hb020/batterymeter/doc/CN0510/EVAL-ADICUP3029/EVAL_ADICUP3029_ID.pdf

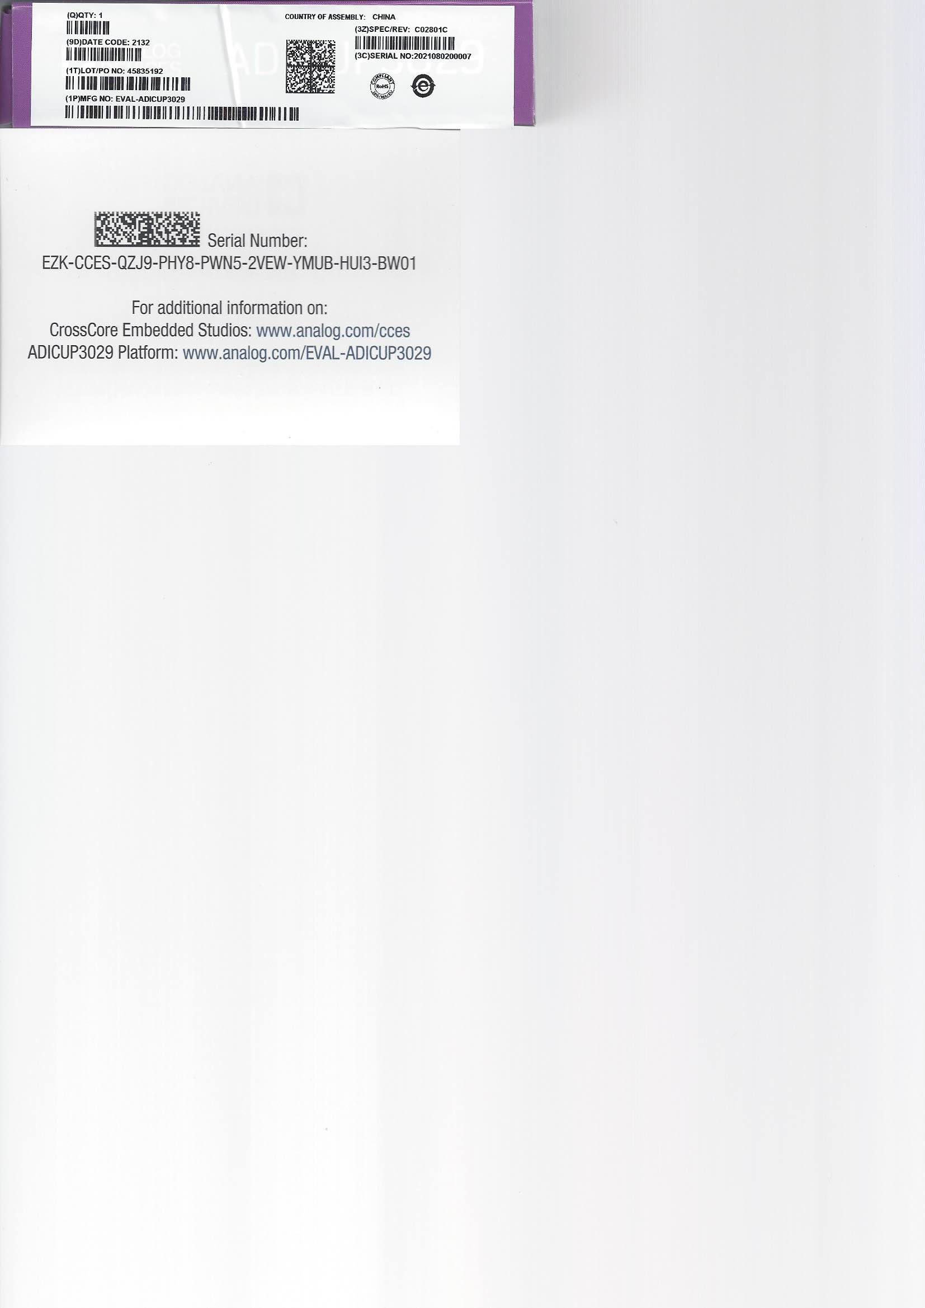
[picture p9: page 1]
