hb020/batterymeter/img/CN0510_06_1024.jpg

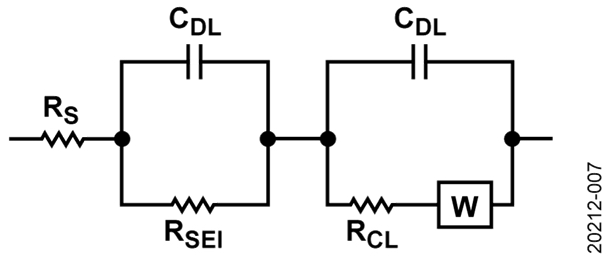
img/CN0510_06_1024.jpg
