hb020/batterymeter/img/pogo-R100-1W.jpg

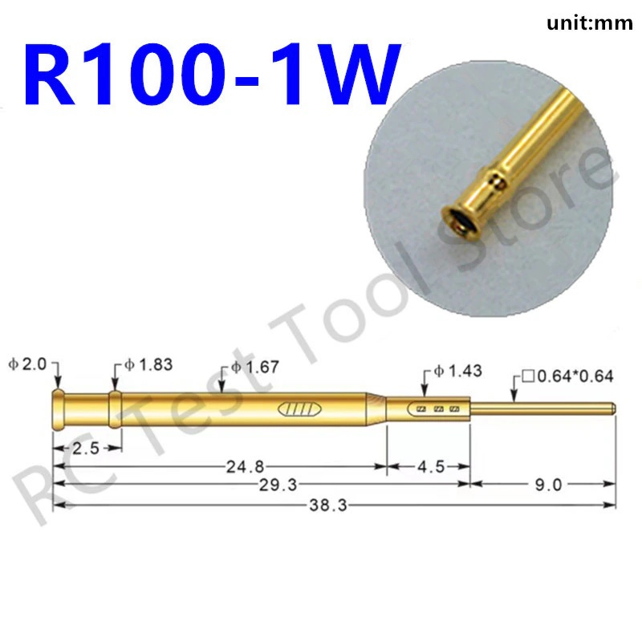
img/pogo-R100-1W.jpg
