hb020/batterymeter/doc/components/oled_128x32/11111782823_523352349.jpeg

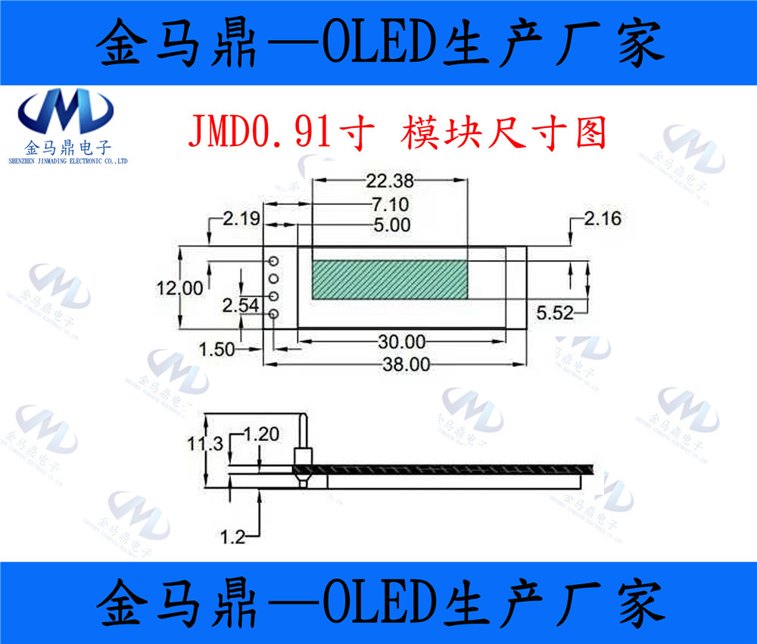
doc/components/oled_128x32/11111782823_523352349.jpeg
