hb020/batterymeter/doc/components/oled_128x32/19966762783_523352349.jpeg

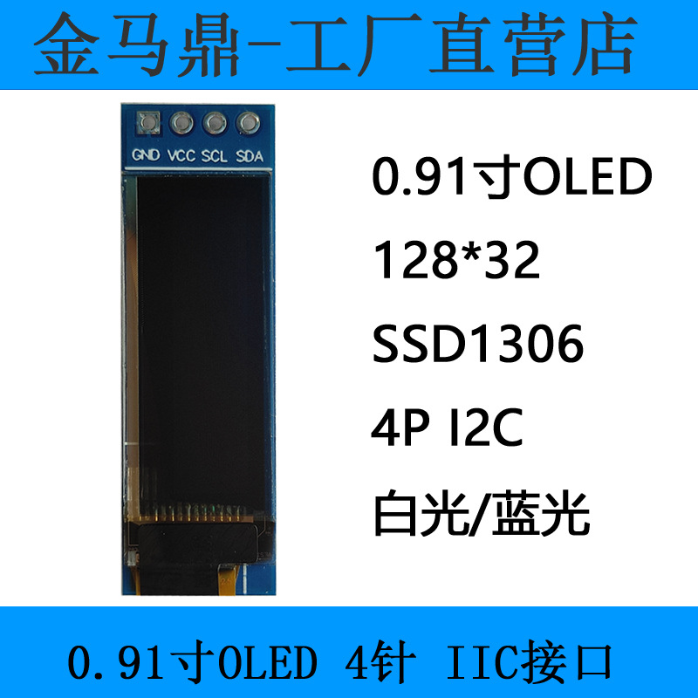
doc/components/oled_128x32/19966762783_523352349.jpeg
