hb020/batterymeter/doc/CN0510/CN0510-DesignSupport/01-047456-01-d.pdf

## ART FILM - assy1

D

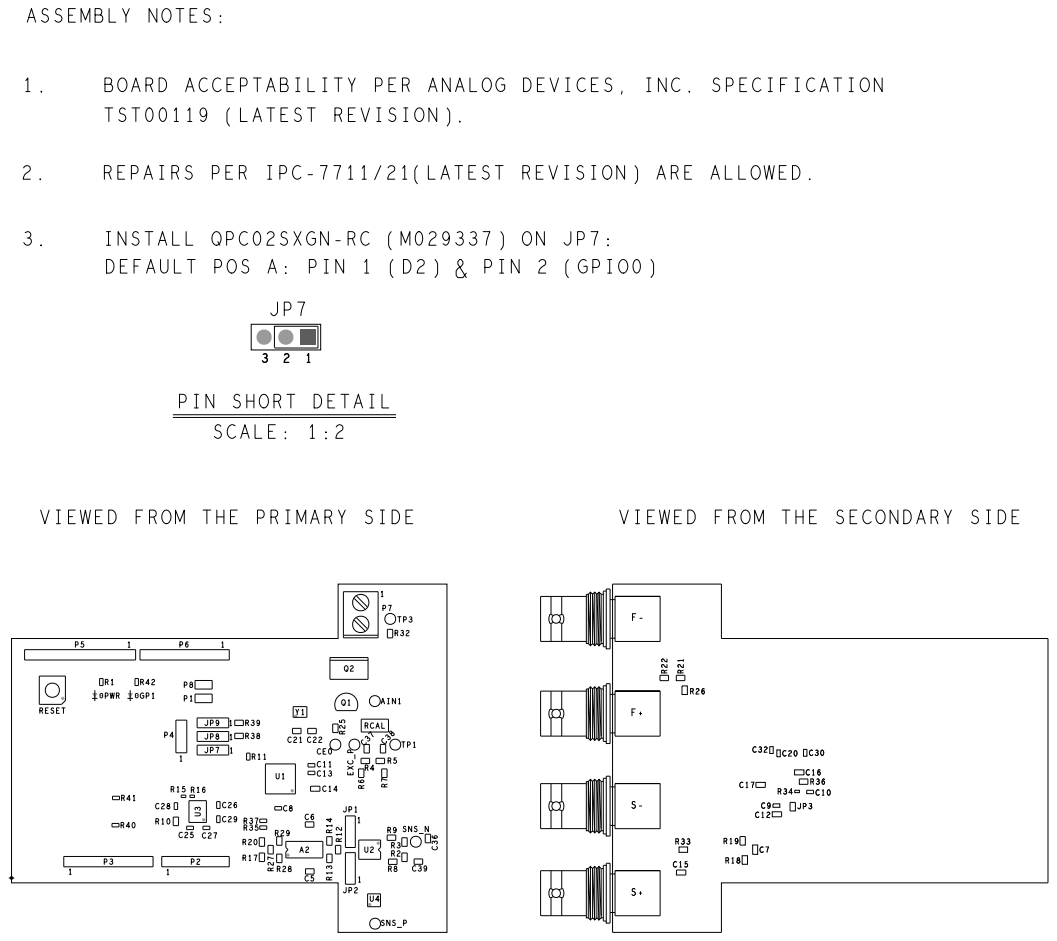
[picture p24: page 1]

REVISIONS

REV | DESCRIPTION | | | DATE | | APPROVED
A | INITIAL RELEASE | | | | 30JAN18 | C.DENG
B | AS PER ECR-078094 | | | | 21MAY18 | C.DENG
C | PER ECR-084889 | 01MAR19 | P SHEAHAN

D | PER ECR-089796 | 16AUG19 | P SHEAHAN

DEFAULT POS A: PIN 1 (D2) & PIN 2 (GPIO0)

VIEWED FROM THE PRIMARY SIDE

VIEWED FROM THE SECONDARY SIDE

UNLESS OTHERWISE SPECIFIED DECIMALS .XX +-.010 .XXX +-.005 .XXXX +-.0050 | TOLERANCES FRACTIONS +-1/32 | ANGLES +- 2 | APPROVAL | DATE

TEMPLATE ENGINEER N/A
HARDWARE SERVICES P SHEAHAN | 16AUG19

MATERIAL | TEST ENGINEER N/A

COMPONENT ENGINEER N/A

TEST PROCESS N/A
HARDWARE RELEASE P SHEAHAN | 16AUG19
DESIGNER M LAMBE | 16AUG19 | SIZE C | FSCM NO 24355 | DRAWING NUMBER 01 | -047456 | REV D
PTD ENGINEER M LAMBE | 16AUG19

CHECKER N/A

DO NOT SCALE DWG | | 1/1 SCALE | | SHEET
