hb020/batterymeter/doc/CN0510/CN0510-DesignSupport/08-047456-01-d.pdf

## ART FILM - silk_prm

047456

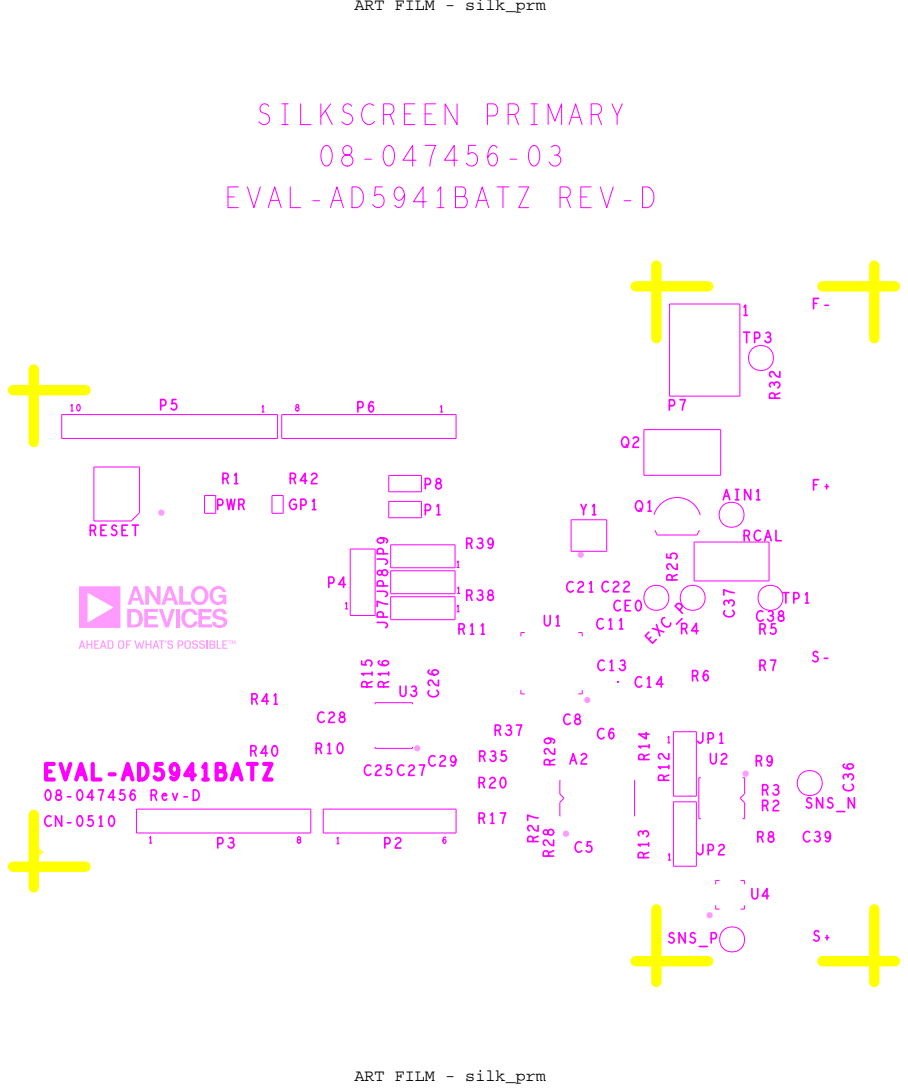
[picture p25: page 1]

## ART FILM - l1_primary

047456

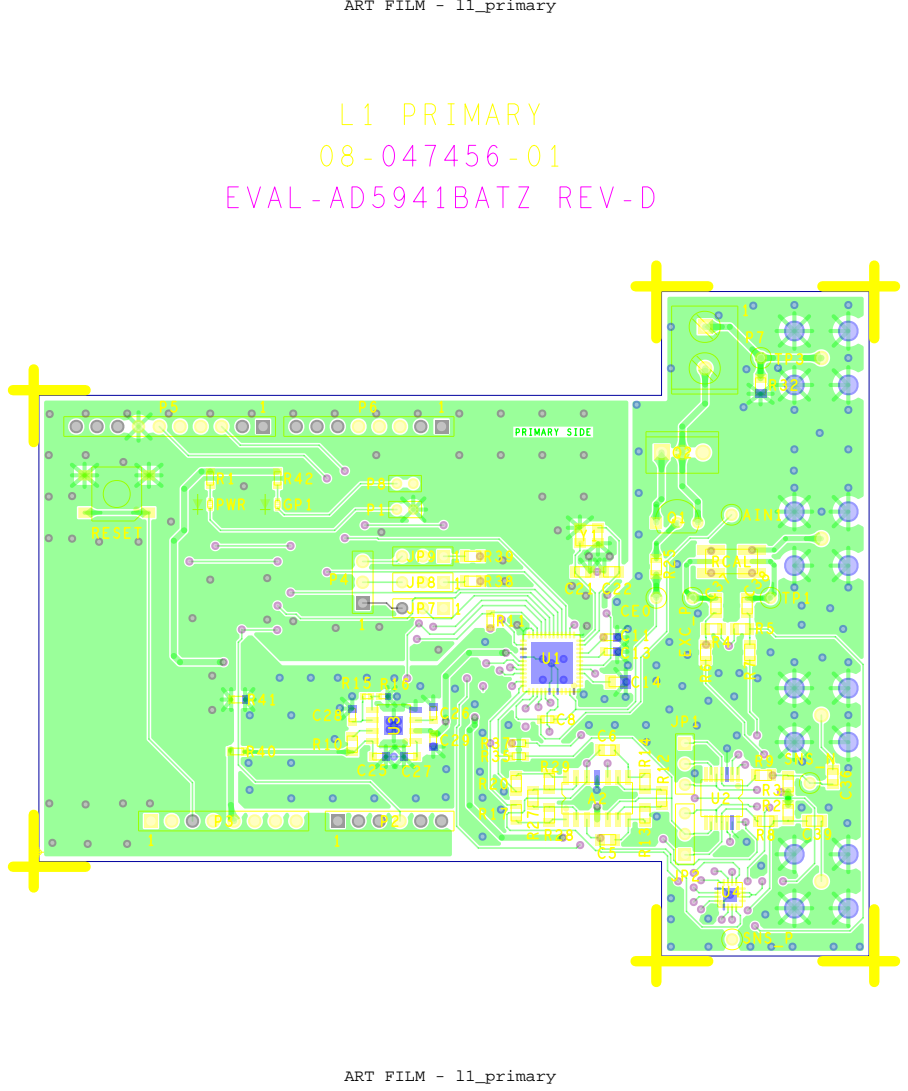
[picture p26: page 2]

## ART FILM - l2_secondary

047456

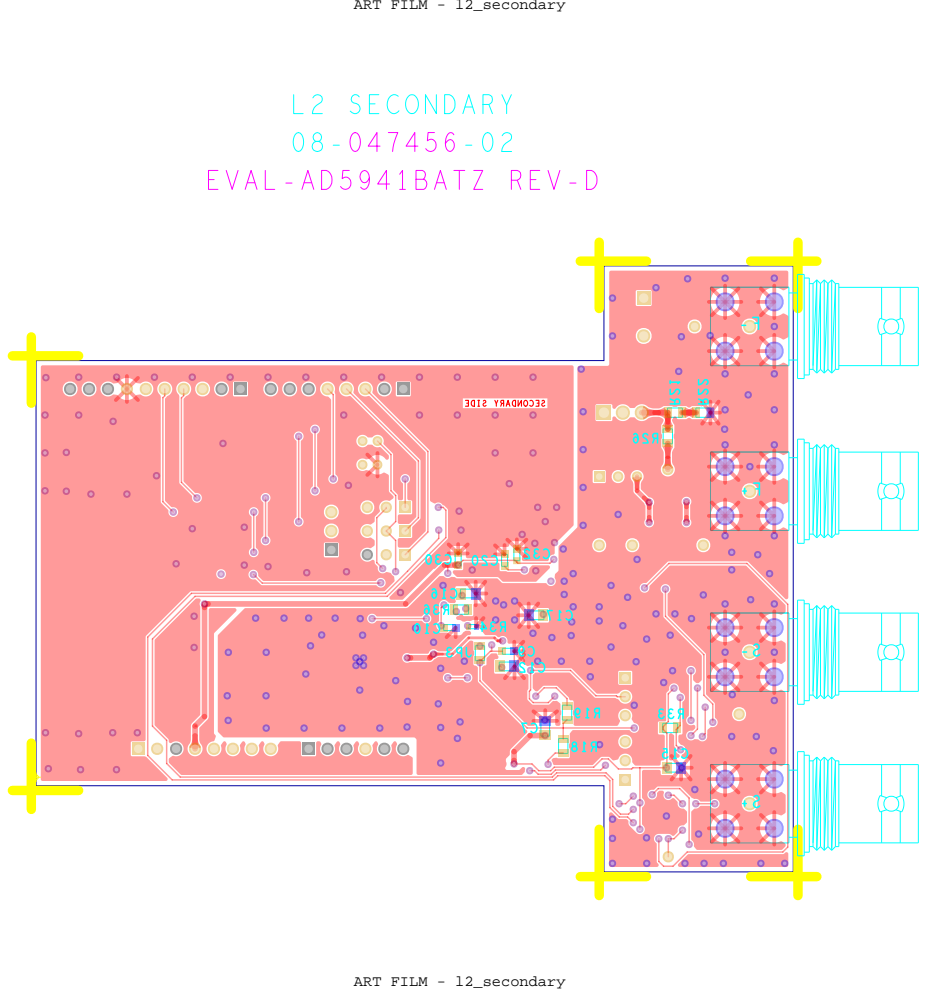
[picture p27: page 3]

## ART FILM - silk_sec

047456

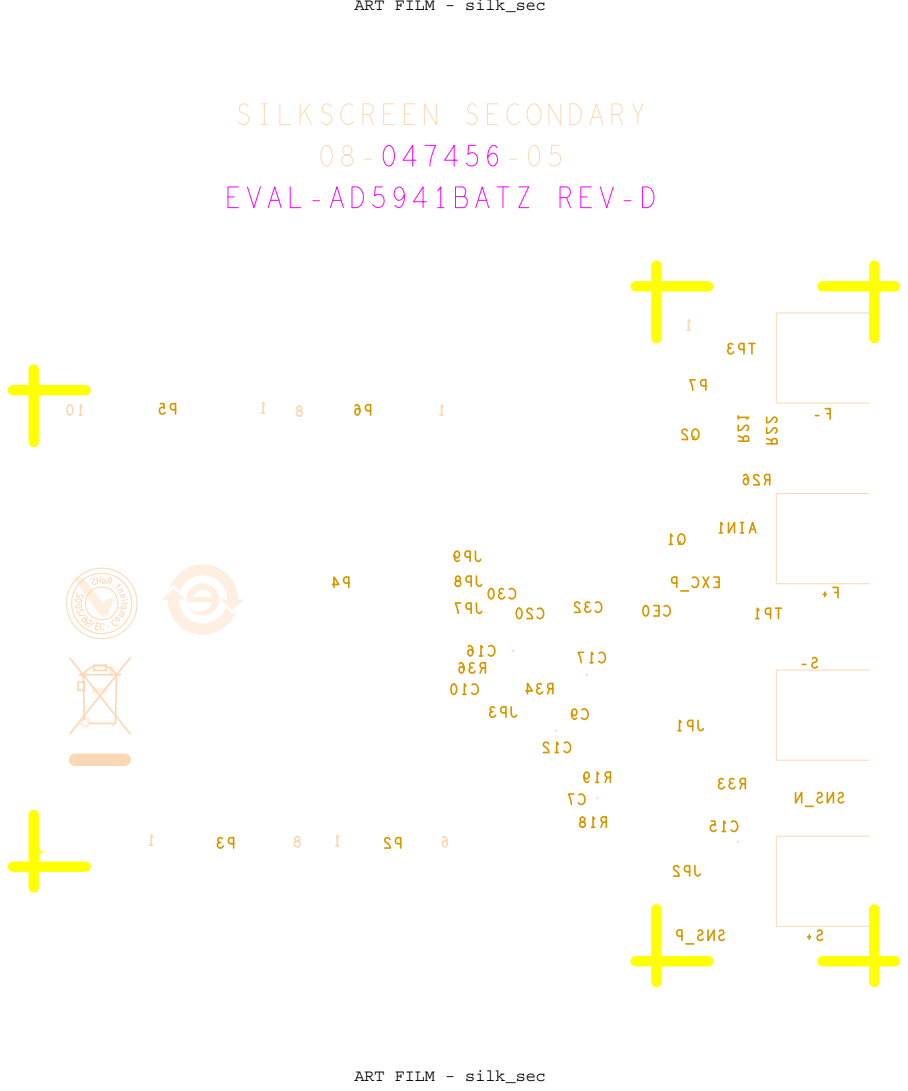
[picture p28: page 4]

## ART FILM - mask_prm

08- | -04 047456

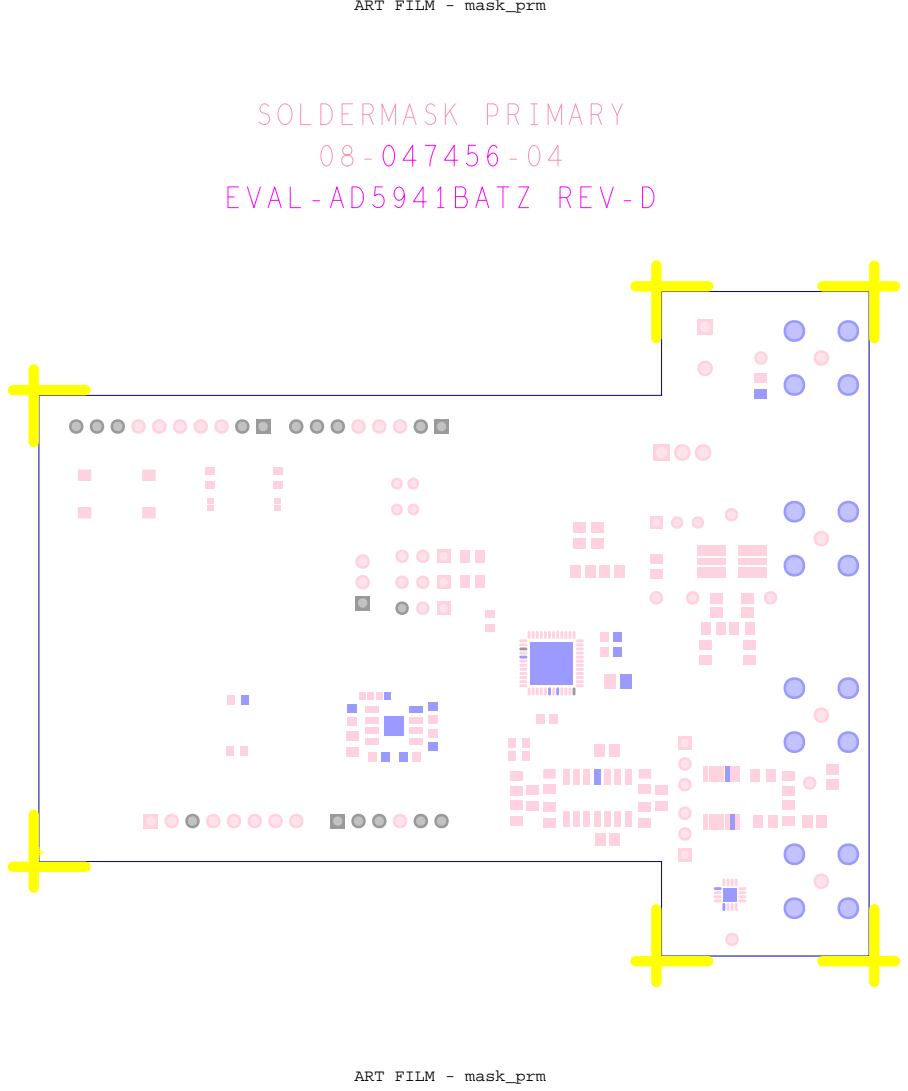
[picture p29: page 5]
ART FILM - mask_prm; SOLDERMASK PRIMARY; EVAL-AD5941BATZ REV-D

## ART FILM - mask_sec

08- | -06 047456

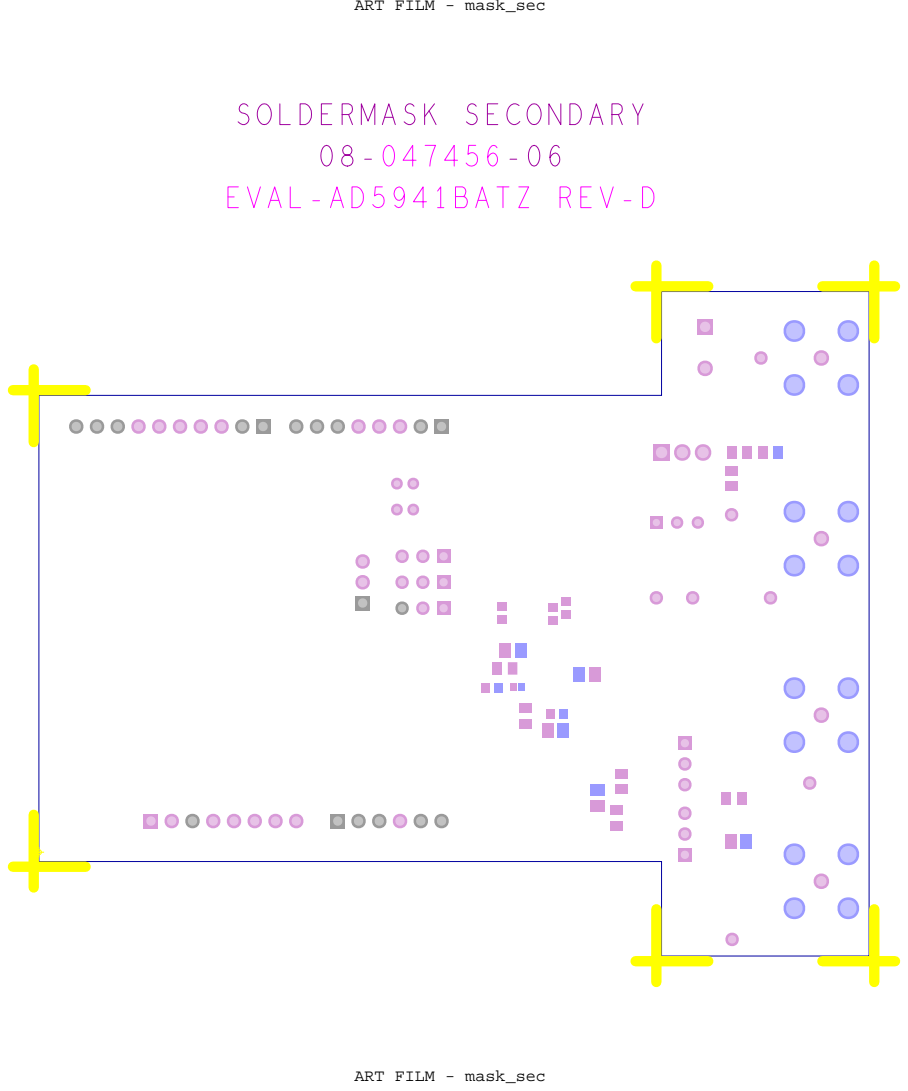
[picture p30: page 6]
ART FILM - mask_sec; SOLDERMASK SECONDARY; EVAL-AD5941BATZ REV-D

## ART FILM - paste_prm

047456

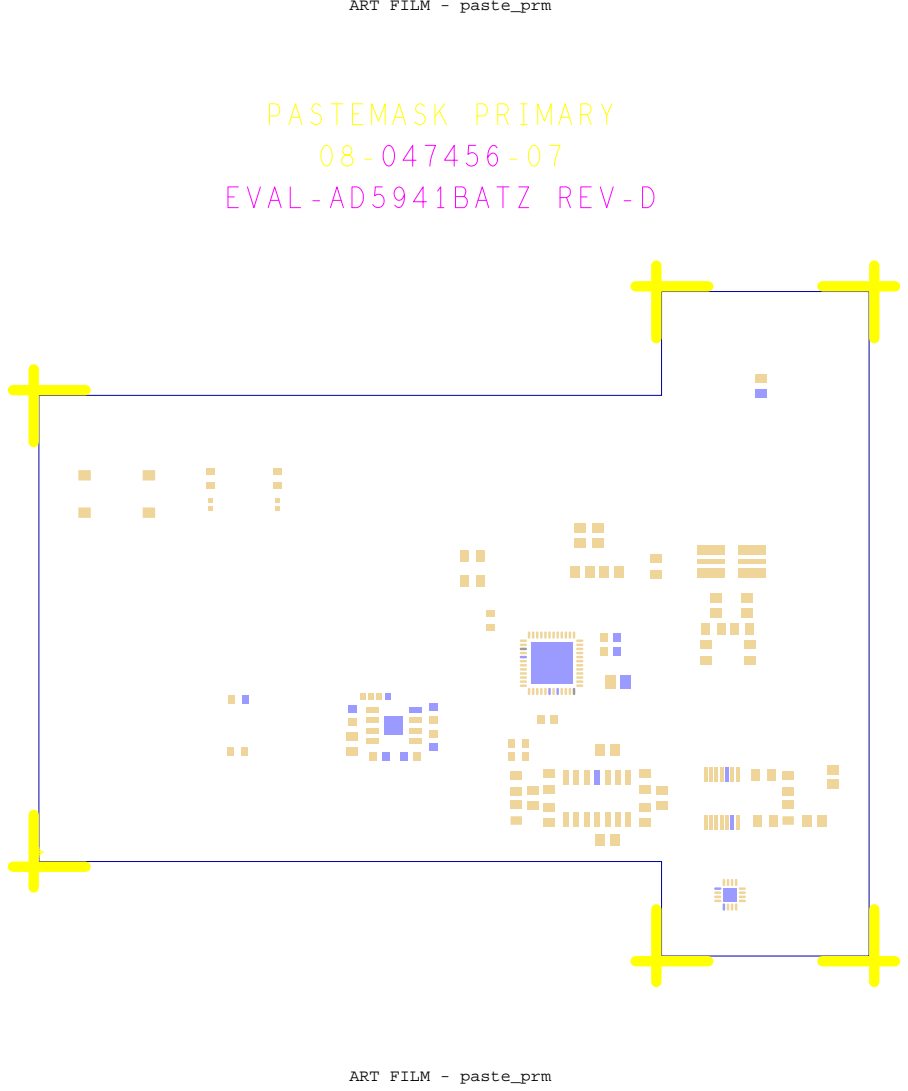
[picture p31: page 7]
ART FILM - paste_prm; PASTEMASK PRIMARY; EVAL-AD5941BATZ REV-D

## ART FILM - paste_sec

## ART FILM - paste_sec

08- | -08 047456

# PASTEMASK SECONDARY

# EVAL-AD5941BATZ REV-D
