hb020/batterymeter/doc/CN0510/CN0510-DesignSupport/09-047456-01-d.pdf

D

1

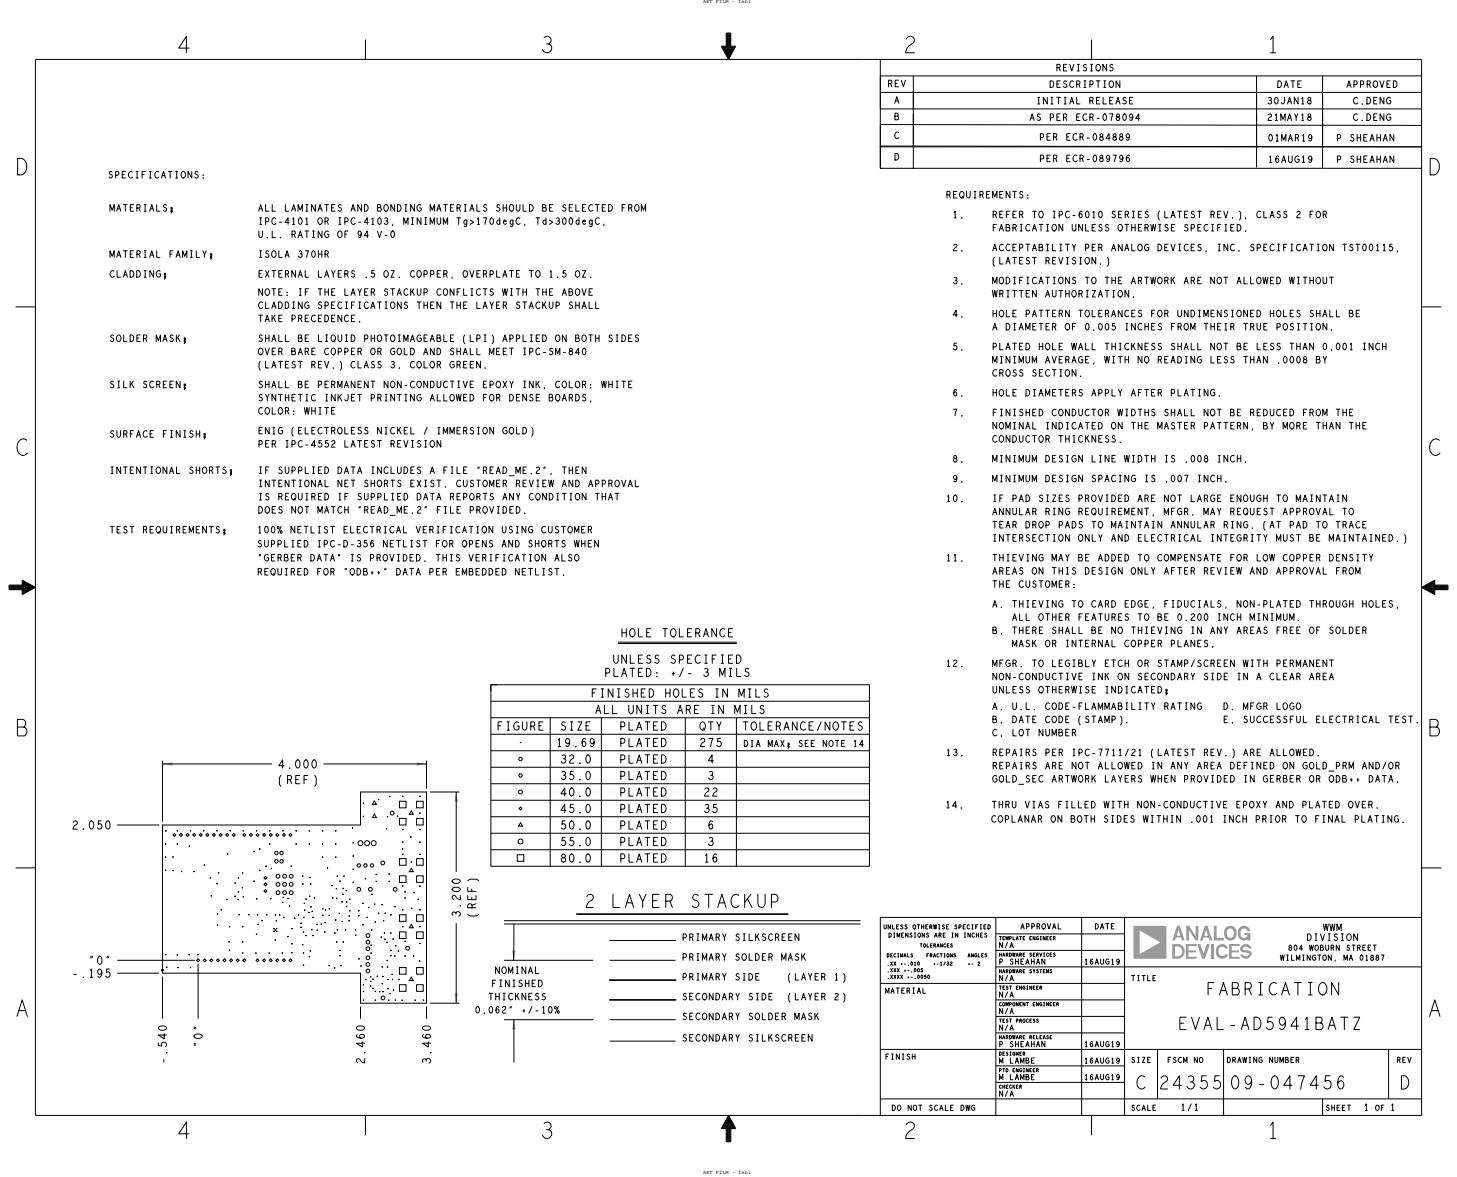
[picture p32: page 1]
ART FILM - fab1; C.DENG; P SHEAHAN; WWM DIVISION 804 WOBURN STREET WILMINGTON, MA 01887; 21MAY18; 01MAR19; 16AUG19; PER ECR-089796; REQUIREMENTS:; REFER; TO IPC-6010 SERIES (LATEST REV.), CLASS 2 FOR; ACCEPTABILITY PER ANALOG DEVICES,; INC. SPECIFICATION; TST00115,; (LATEST REVISION.); MODIFICATIONS; THE ARTWORK ARE NOT ALLOWED WITHOUT; WRITTEN AUTHORIZATION.; HOLE PATTERN; TOLERANCES FOR UNDIMENSIONED; HOLES SHALL BE; A DIAMETER OF 0.005; INCHES FROM; THEIR; TRUE POSITION.; PLATED; HOLE WALL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

REVISIONS

REV | DESCRIPTION | DATE | | APPROVED
A | INITIAL RELEASE | | 30JAN18 | C.DENG

AS PER ECR-078094
PER ECR-084889

ALL LAMINATES AND BONDING MATERIALS SHOULD BE SELECTED FROM
U.L. RATING OF 94 V-0
ISOLA 370HR
TAKE PRECEDENCE.
SHALL BE LIQUID PHOTOIMAGEABLE (LPI) APPLIED ON BOTH SIDES
(LATEST REV.) CLASS 3. COLOR GREEN.
SYNTHETIC INKJET PRINTING ALLOWED FOR DENSE BOARDS,
COLOR: WHITE
PER IPC-4552 LATEST REVISION

FABRICATION UNLESS OTHERWISE SPECIFIED.

6. HOLE DIAMETERS APPLY AFTER PLATING.

INTENTIONAL NET SHORTS EXIST. CUSTOMER REVIEW AND APPROVAL
DOES NOT MATCH "READ_ME.2" FILE PROVIDED.
100% NETLIST ELECTRICAL VERIFICATION USING CUSTOMER
SUPPLIED IPC-D-356 NETLIST FOR OPENS AND SHORTS WHEN
"GERBER DATA" IS PROVIDED. THIS VERIFICATION ALSO
REQUIRED FOR "ODB++" DATA PER EMBEDDED NETLIST.

AREAS ON THIS DESIGN ONLY AFTER REVIEW AND APPROVAL FROM
THE CUSTOMER:

HOLE TOLERANCE
UNLESS SPECIFIED
PLATED: +/- 3 MILS
ALL UNITS ARE IN MILS
PLATED
2 LAYER STACKUP

UNLESS OTHERWISE INDICATED;
C. LOT NUMBER

13. REPAIRS PER IPC-7711/21 (LATEST REV.) ARE ALLOWED.

14. THRU VIAS FILLED WITH NON-CONDUCTIVE EPOXY AND PLATED OVER.

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

PRIMARY SILKSCREEN
PRIMARY SOLDER MASK
SECONDARY SIDE (LAYER 2)
SECONDARY SOLDER MASK

TEMPLATE ENGINEER N/A
HARDWARE SERVICES P SHEAHAN | 16AUG19
HARDWARE SYSTEMS N/A | | | TITLE FABRICATION EVAL-AD5941BATZ

MATERIAL | | TEST ENGINEER N/A

COMPONENT ENGINEER N/A

TEST PROCESS N/A
HARDWARE RELEASE P SHEAHAN | 16AUG19
DESIGNER M LAMBE | 16AUG19 | SIZE C | | FSCM NO 24355 | DRAWING NUMBER 09 | -047456 | REV D
PTD ENGINEER M LAMBE | 16AUG19

CHECKER N/A

DO NOT SCALE DWG | | | 1/1 SCALE | | SHEET
