hb020/batterymeter/kicad/impedance_testboard/impedance_testboard_board.pdf

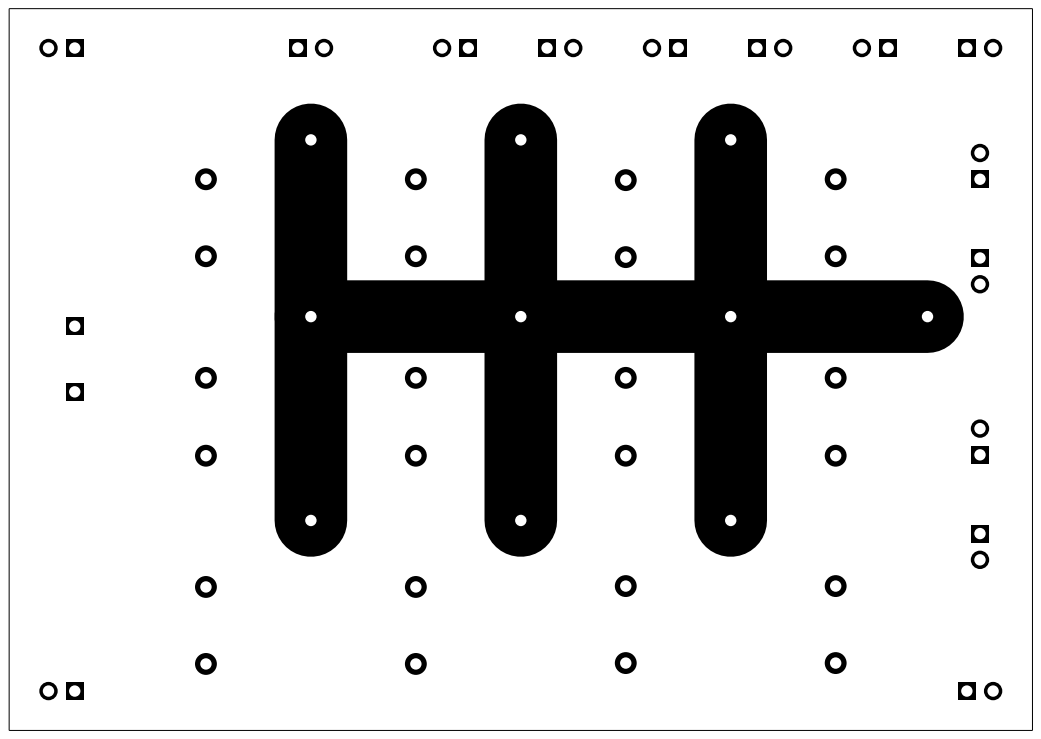
[picture p33: page 1]

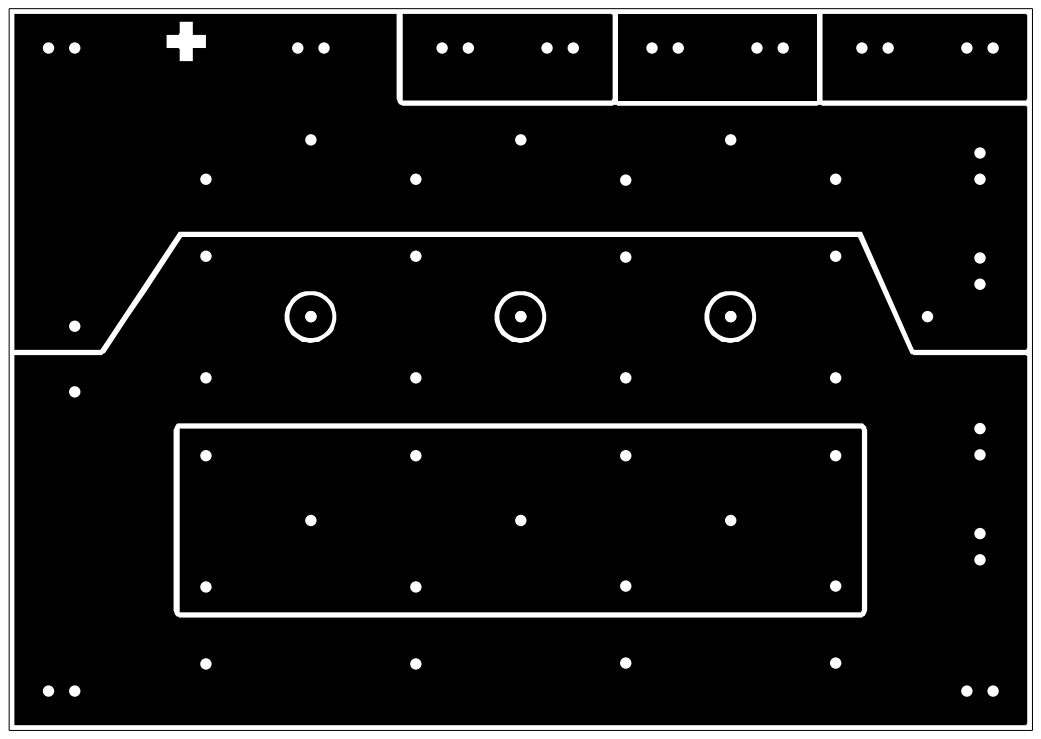
[picture p34: page 2]

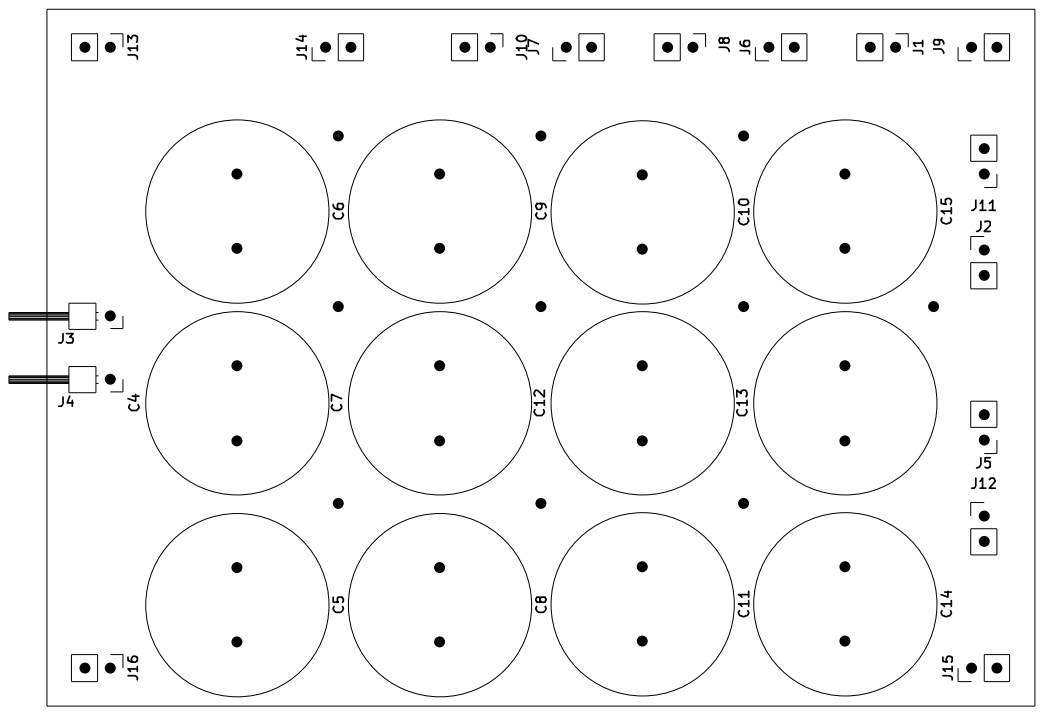
[picture p35: page 3]

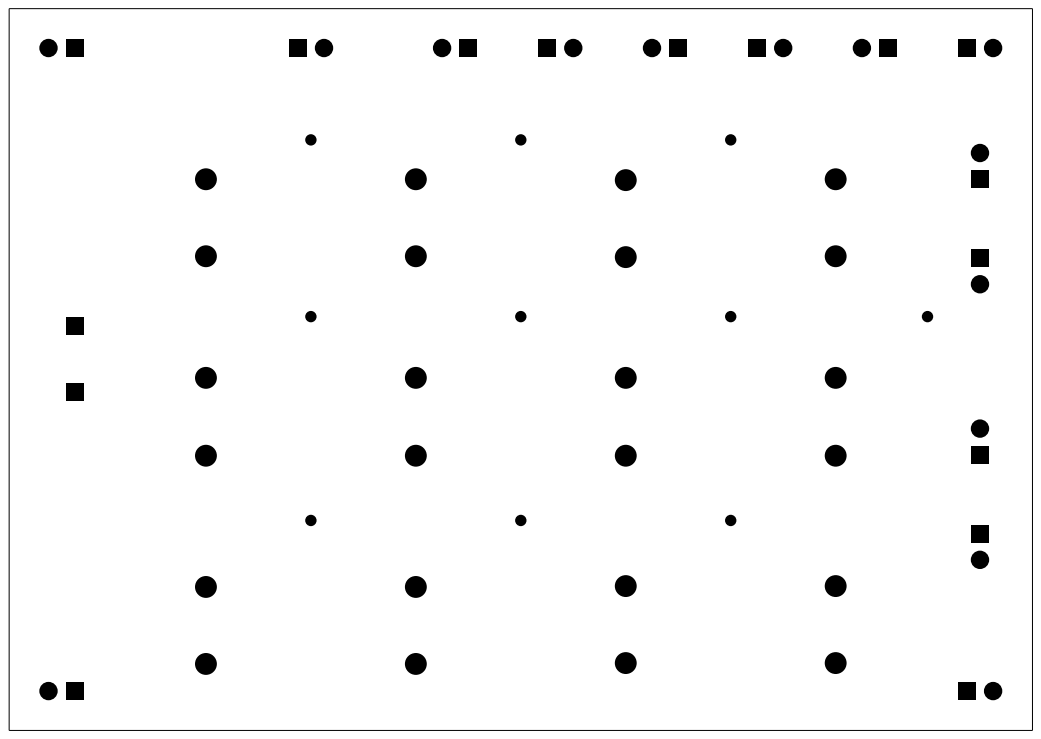
[picture p36: page 4]

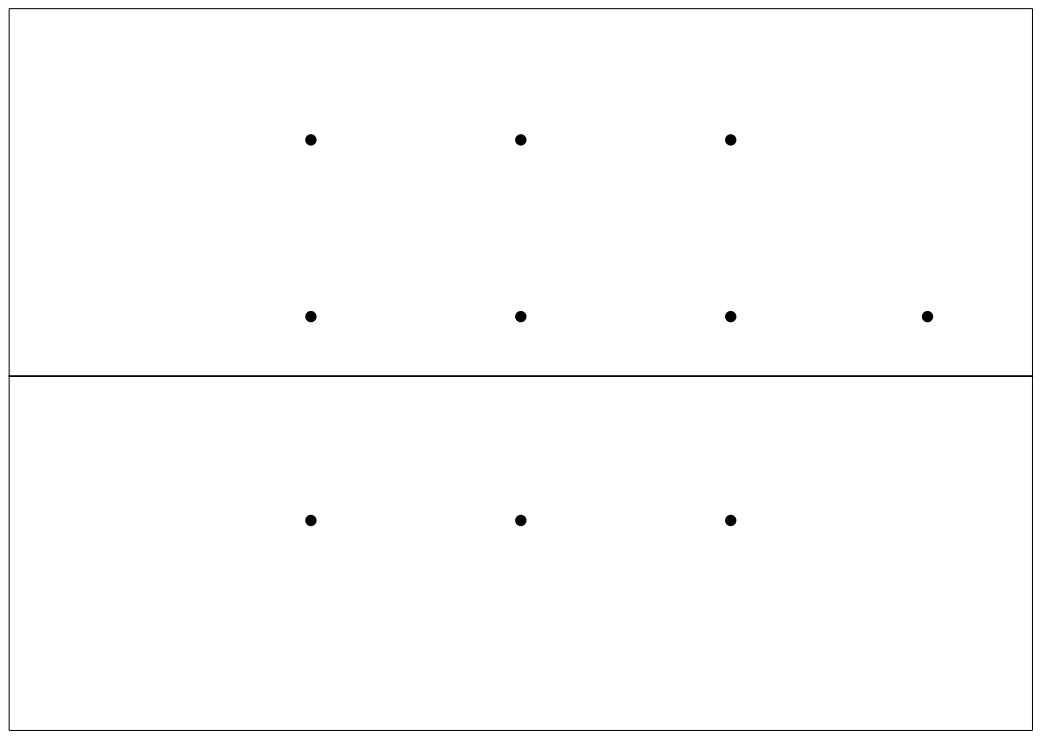
[picture p37: page 5]

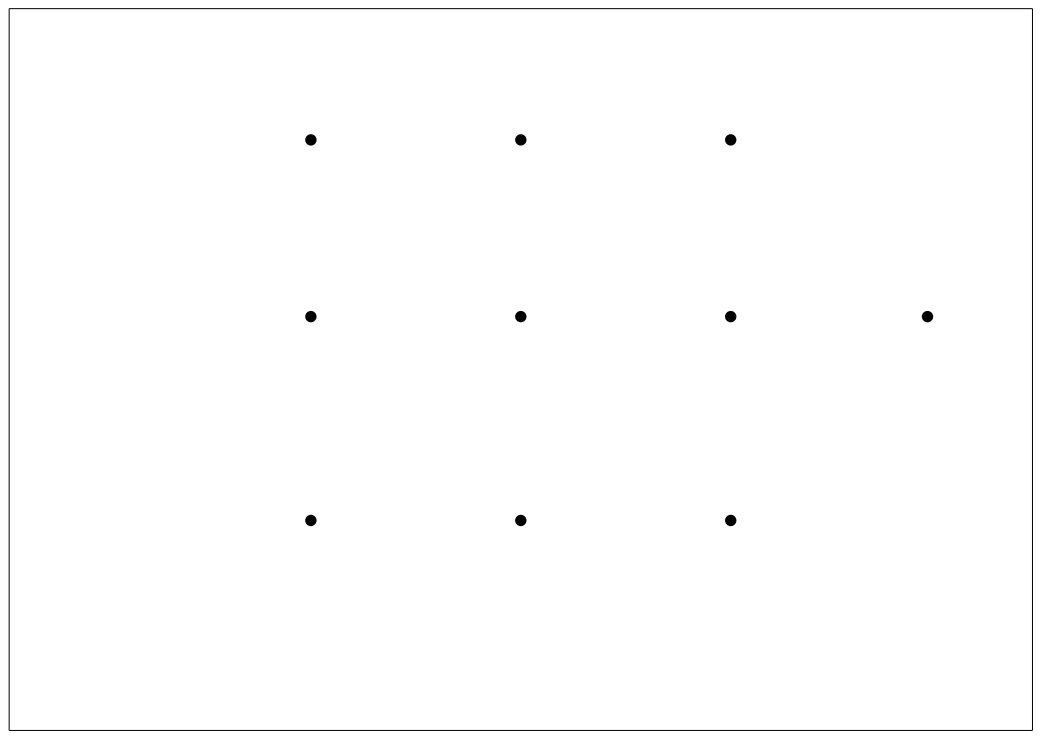
[picture p38: page 6]

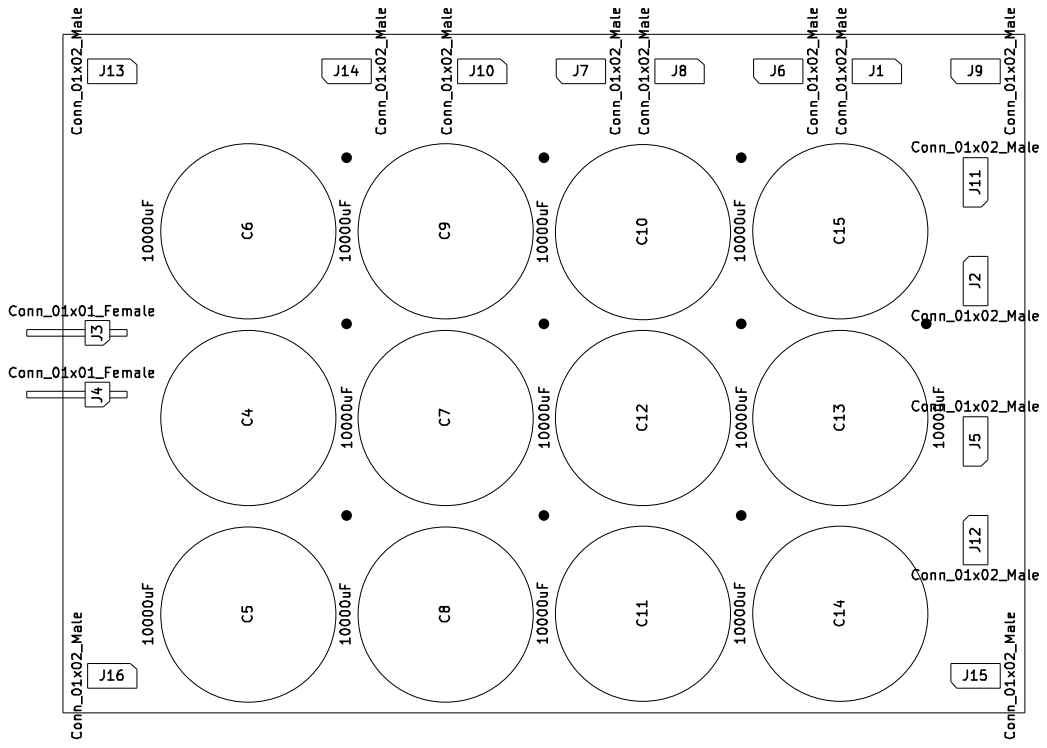
[picture p39: page 8]
