hb020/batterymeter/kicad/impedance_testboard/impedance_testboard_schema.pdf

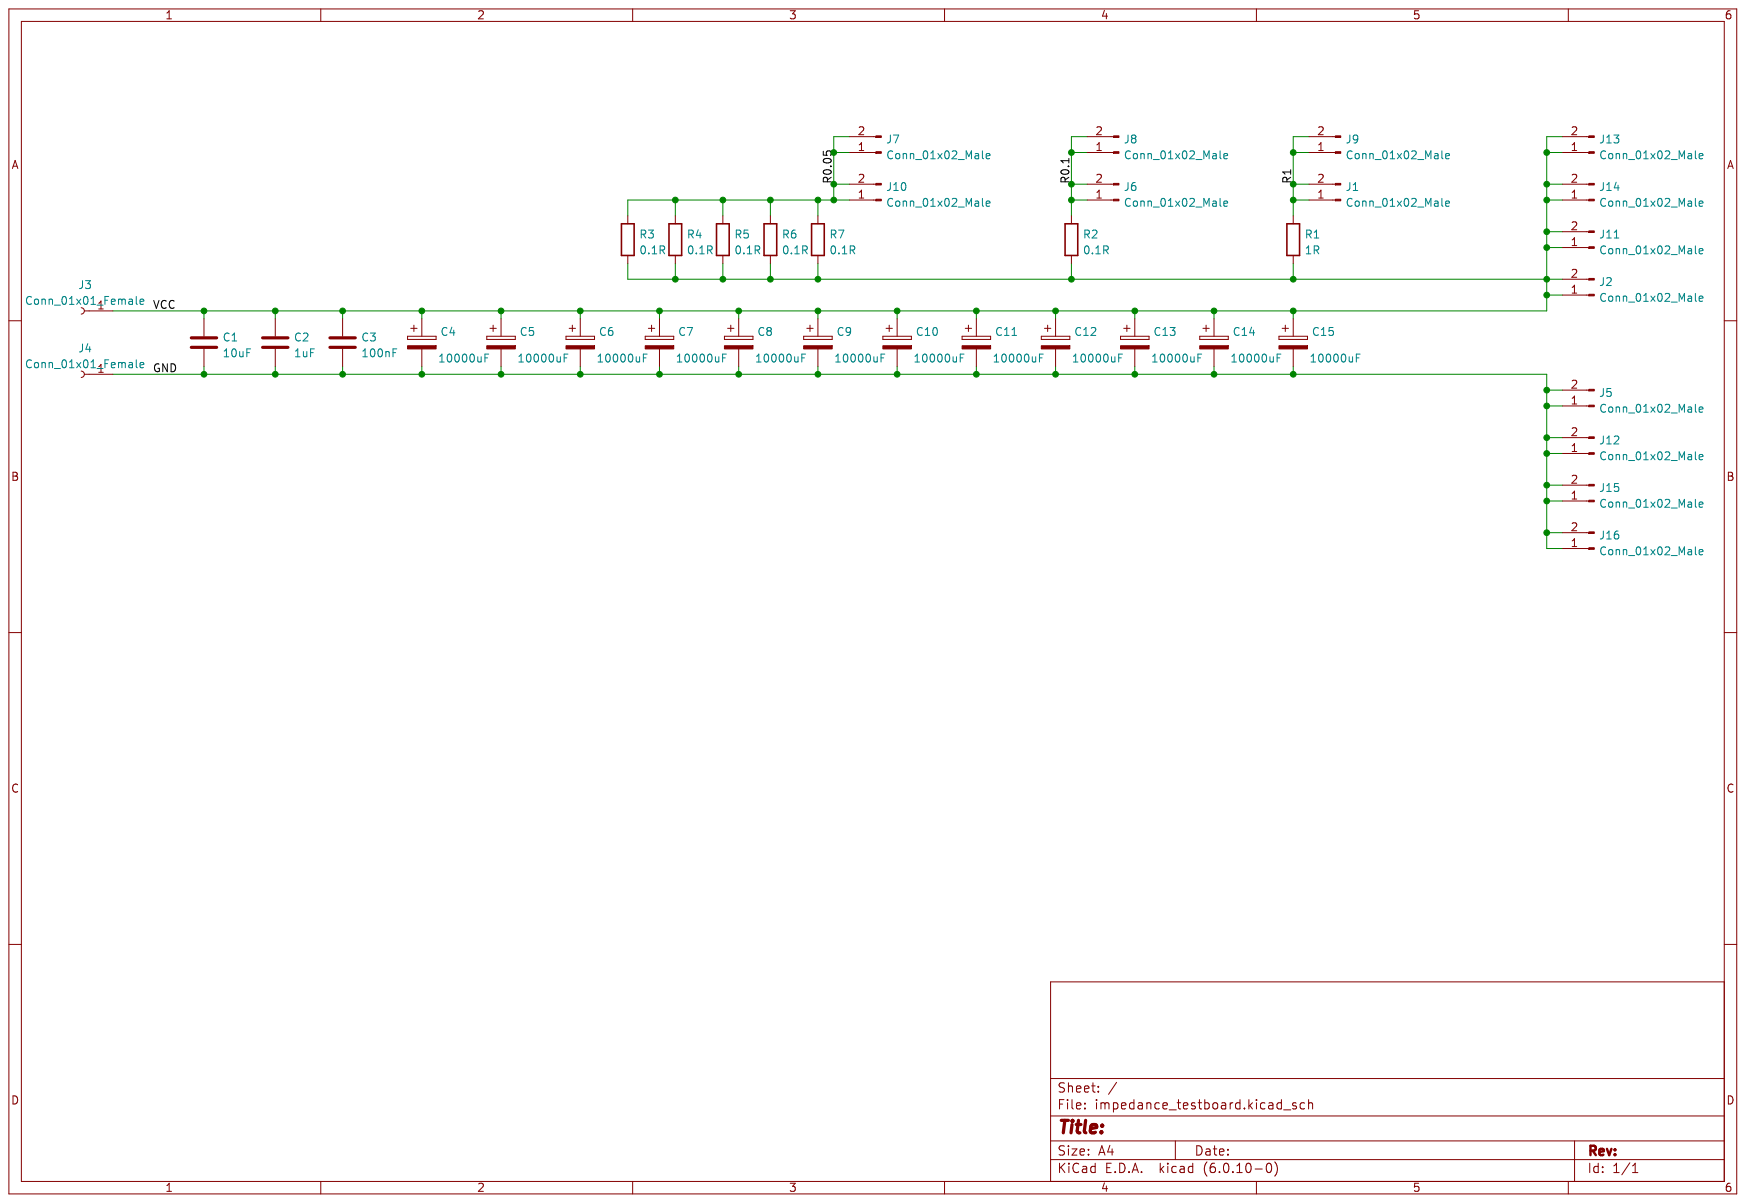
[picture p40: page 1]
