hb020/batterymeter/kicad/batterymeter/batterymeter_schema.pdf

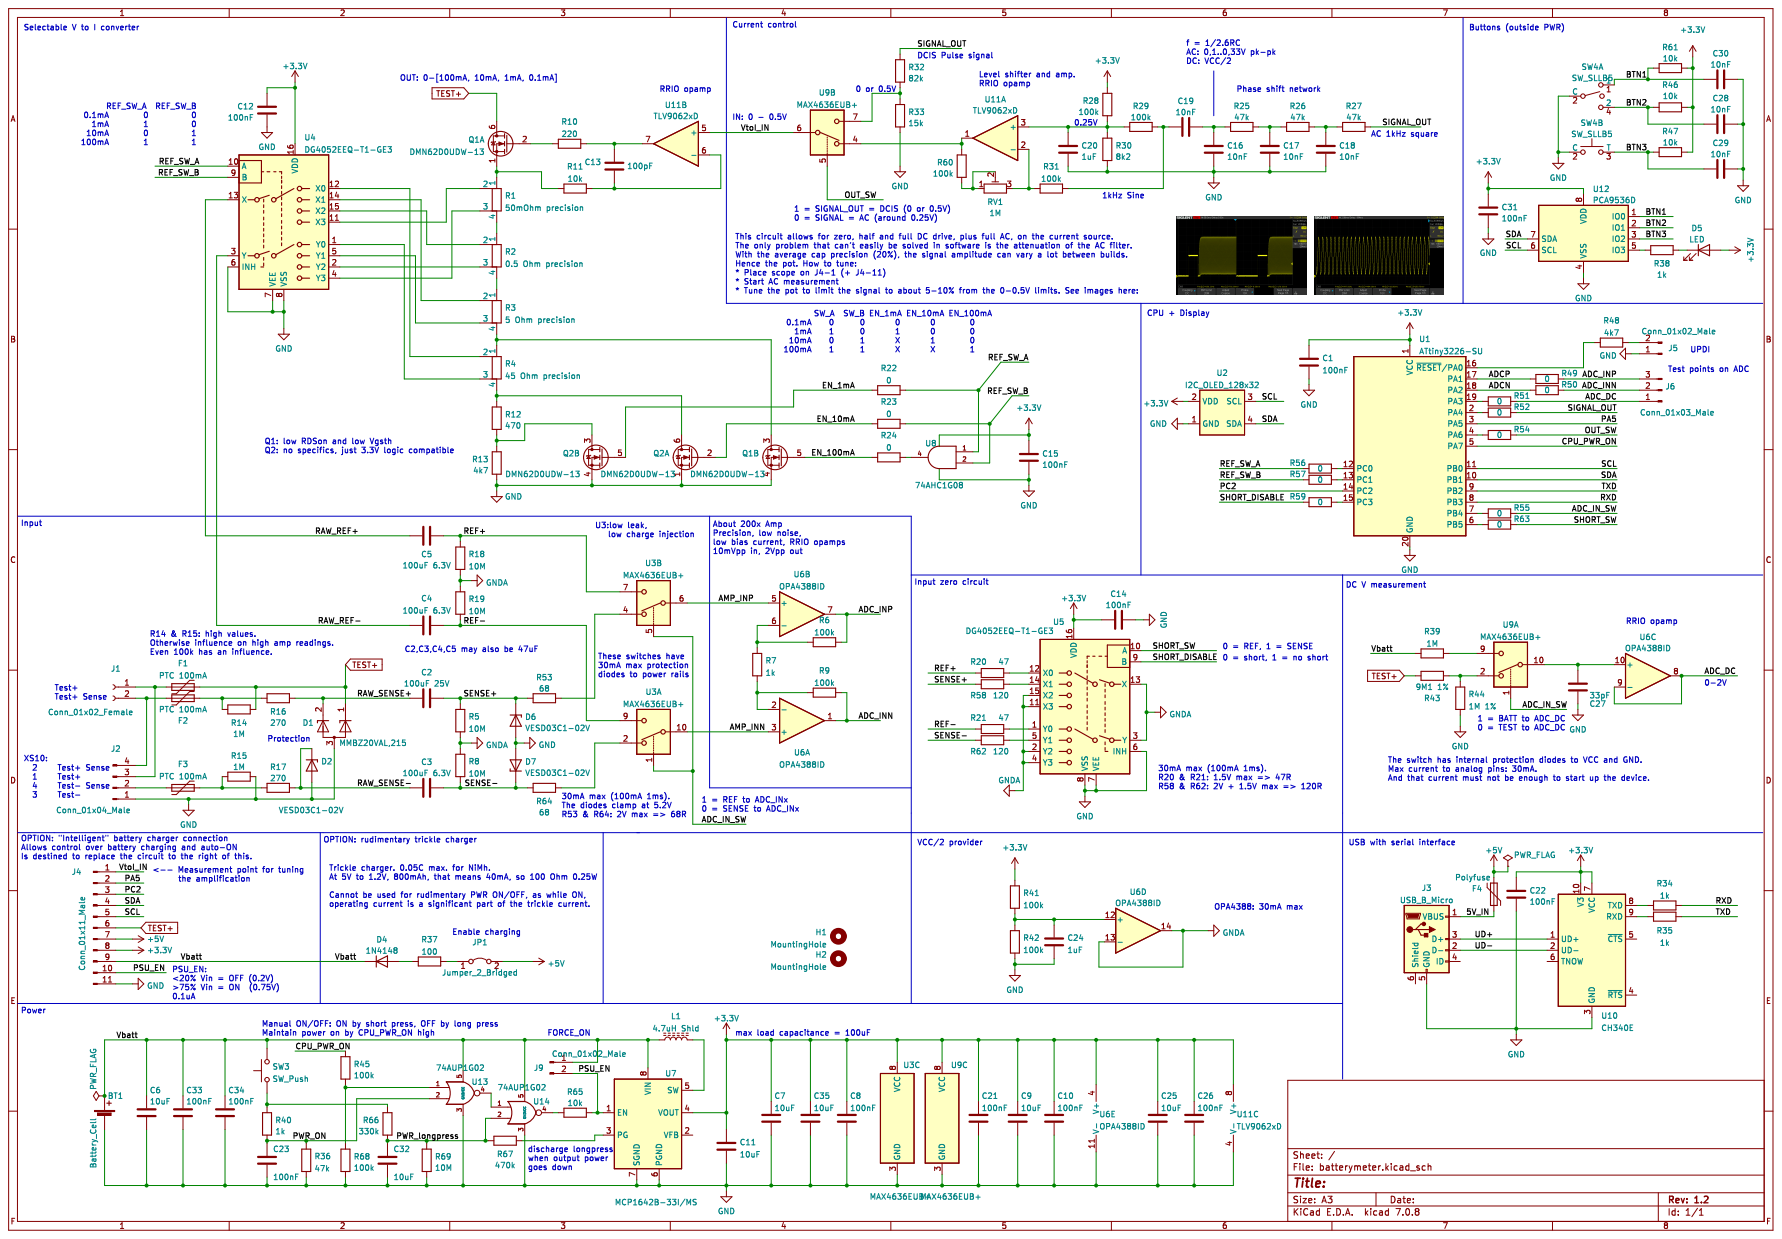
[picture p41: page 1]
