hb020/batterymeter/kicad/batterymeter/batterymeter_board.pdf

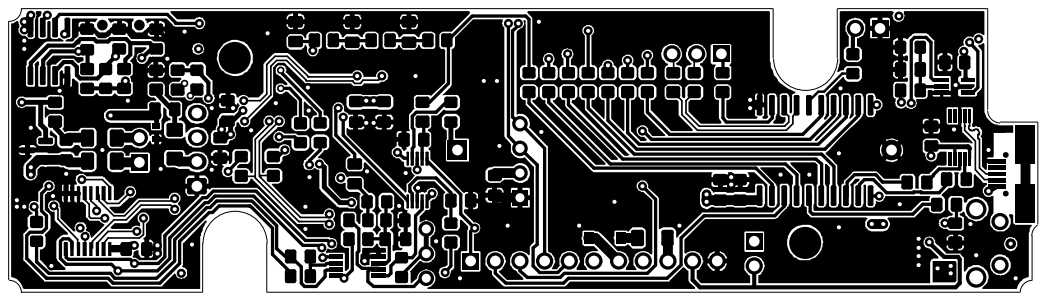
[picture p42: page 1]

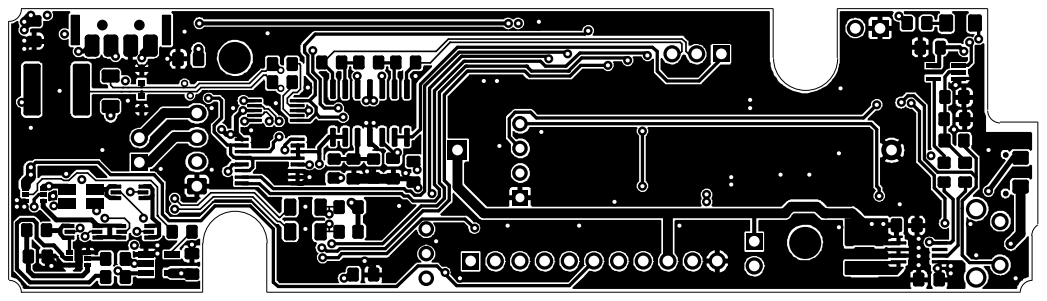
[picture p43: page 2]

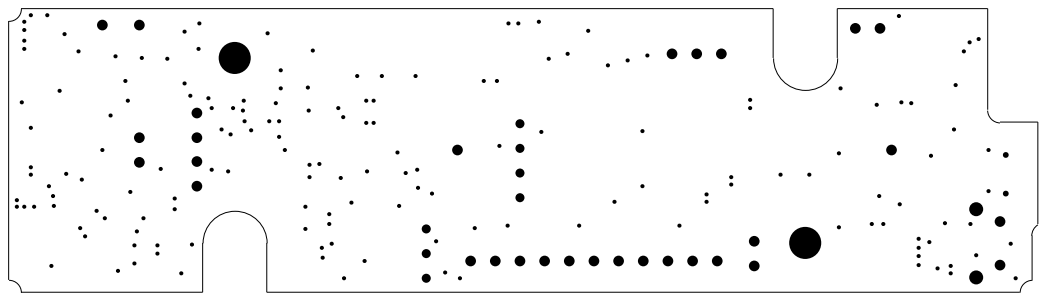
[picture p44: page 3]

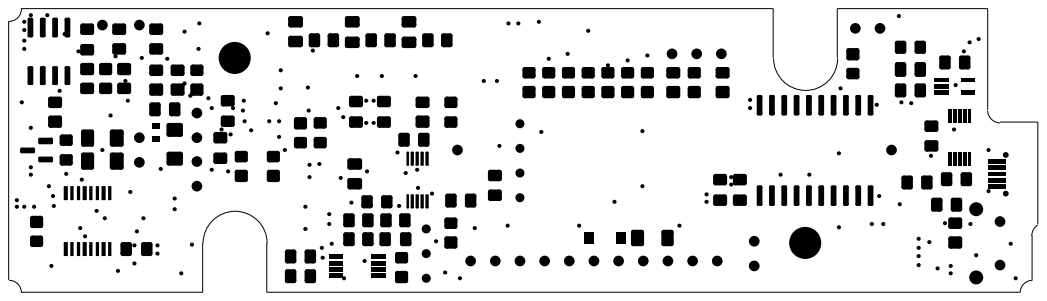
[picture p45: page 5]

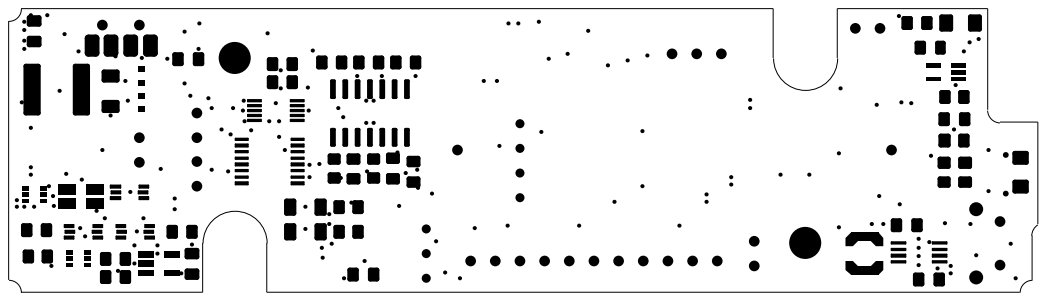
[picture p46: page 6]

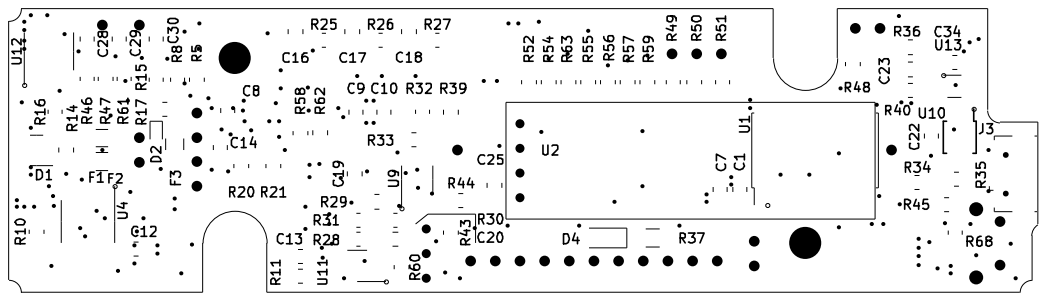
[picture p47: page 7]

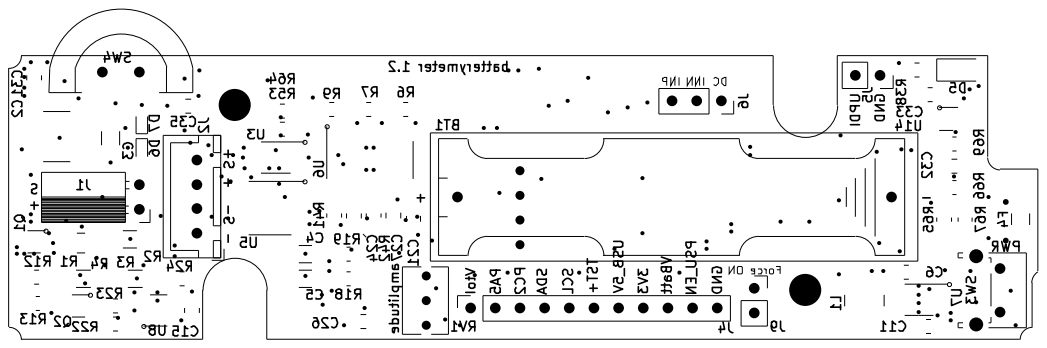
[picture p48: page 8]

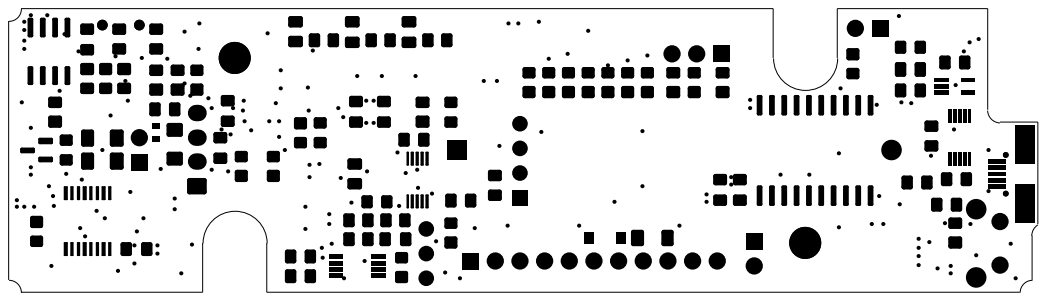
[picture p49: page 9]

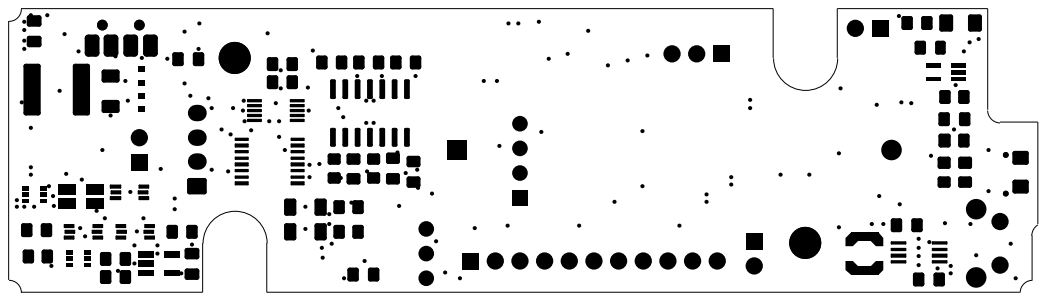
[picture p50: page 10]

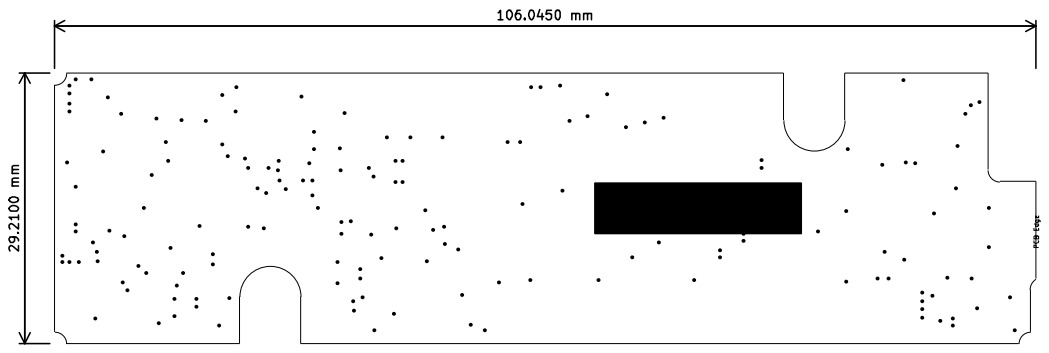
[picture p51: page 11]

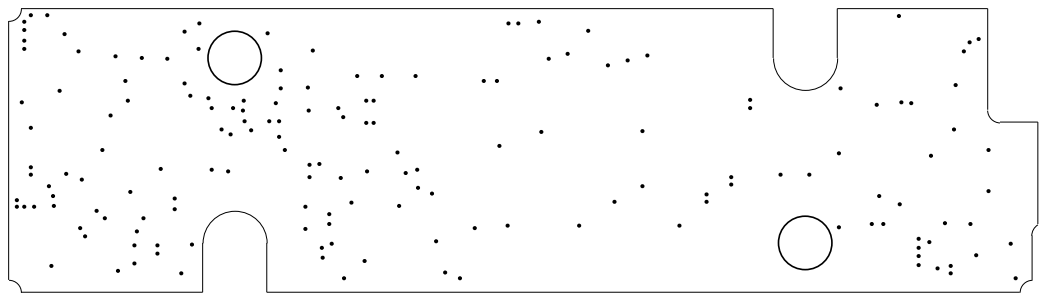
[picture p52: page 12]

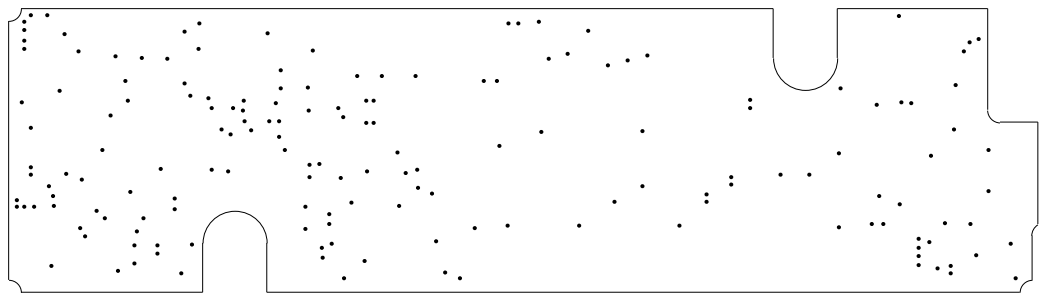
[picture p53: page 13]

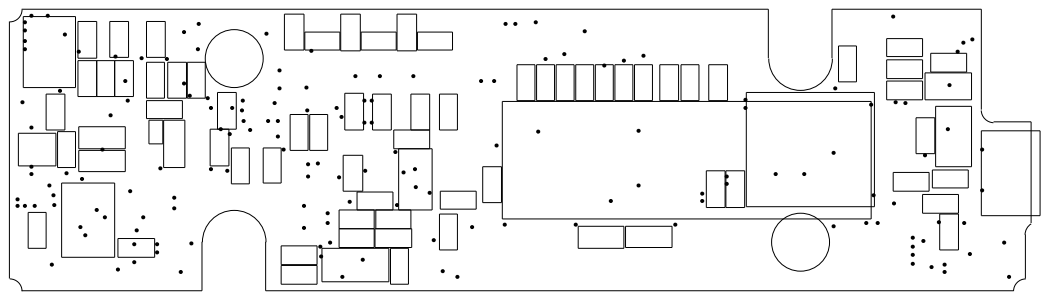
[picture p54: page 17]

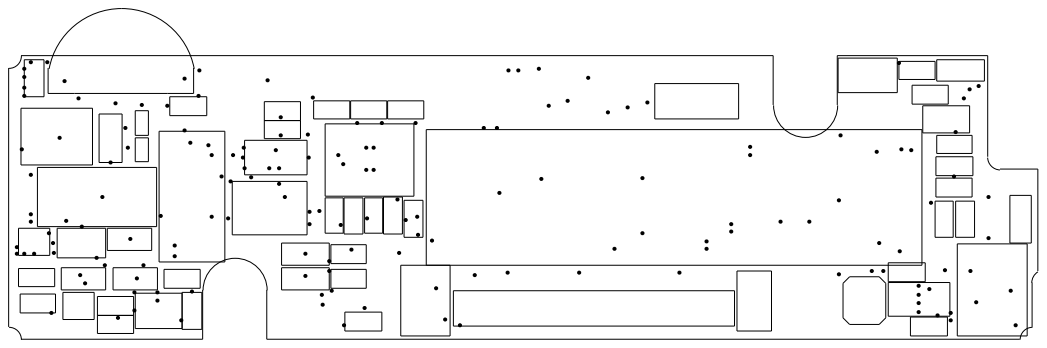
[picture p55: page 18]

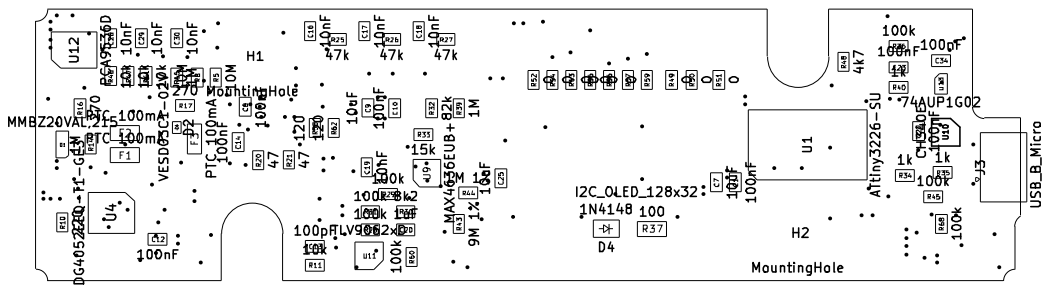
[picture p56: page 19]

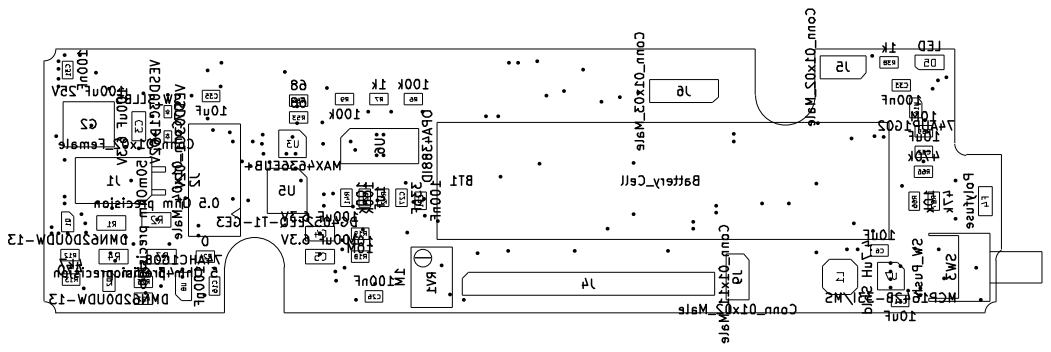
[picture p57: page 20]
