hb020/batterymeter/kicad/YR1035Plus/YR1035Plus_input_schema.pdf

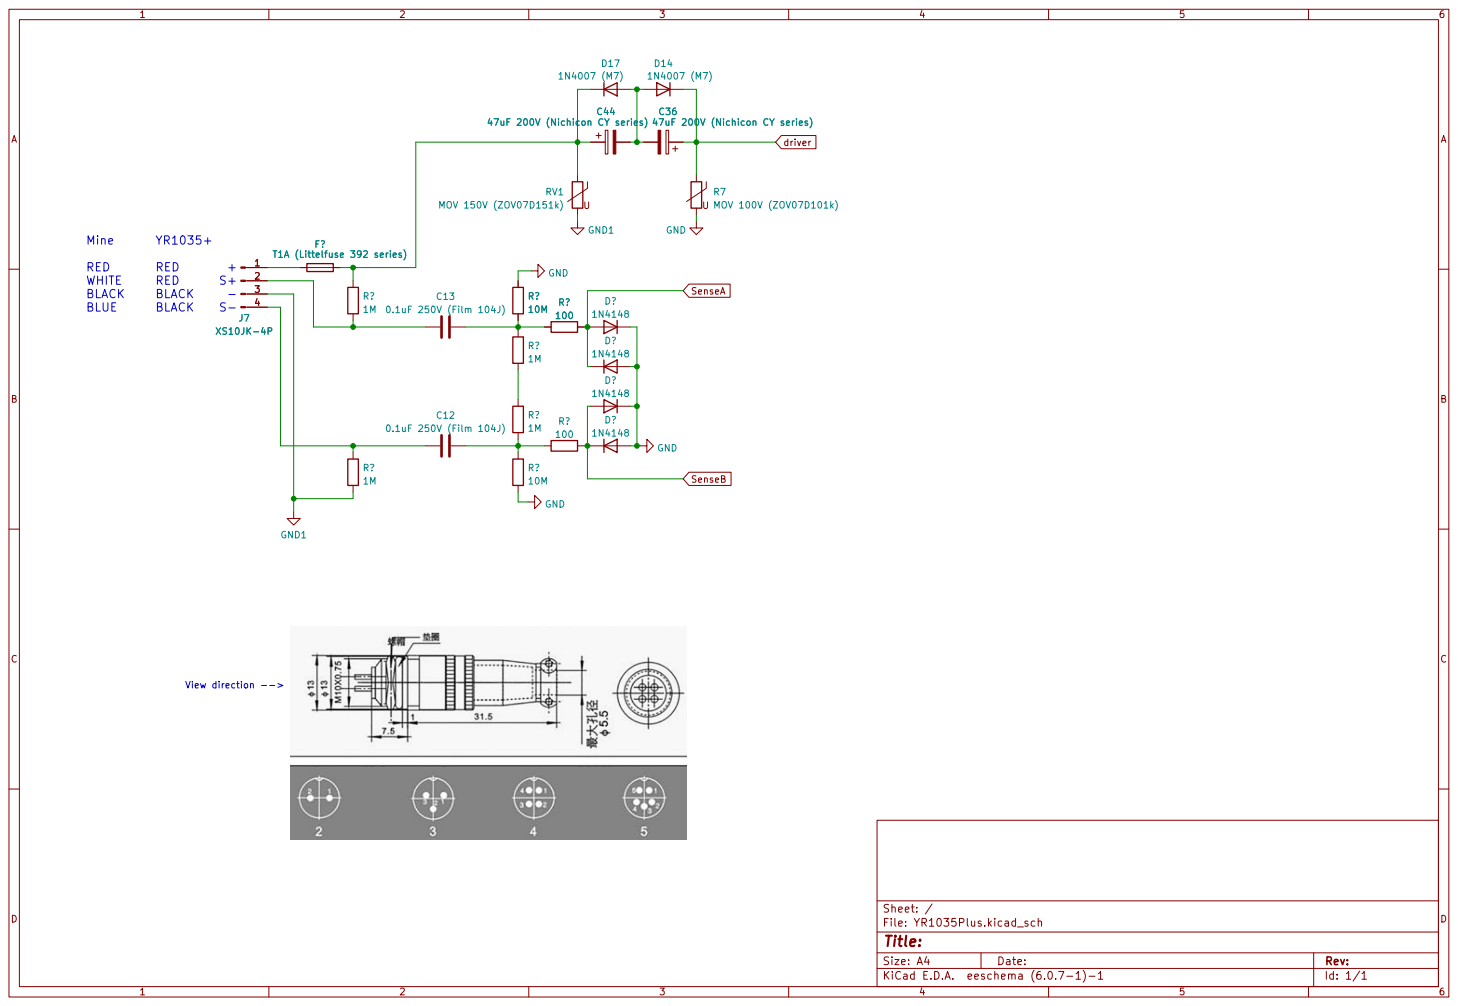
[picture p58: page 1]
