hb020/batterymeter/ltspice/4Winfluence.asc

C1: cap; 100p
M1: nmos; DMN62D0UDW
M2: nmos; DMN62D0UDW
M3: nmos; DMN62D0UDW
M4: nmos; DMN62D0UDW
R1: res; 220
R2: res; 50m
R3: res; 450
R4: res; 4500
R5: res; 5
R6: res; 10k
R7: res; 0.5
R8: res; 10
R9: res; 10
R10: res; 45
R11: res; 100
R12: res; 100
U1: opamp2; TLV9062
V1: voltage; 3; Rser=50m
V2: voltage; 0
V3_1mA: voltage; 3
V4_10mA: voltage; 3
V5: voltage; 3.3
V6: voltage; SINE(0.25 0.25 1k 1f)
V7: voltage; ""; AC 1
V8_100mA: voltage; 3
Named nets: 0, A, B, RefP, RefN, SenseP, SenseN
.tran 2ms
.ac dec 100 1 1MEG
AC test: 
V7 = AC 1
V(A)/V(B)
Distortion: 
I(V1)+I(R5) or .. R10
R6/C1/R1/DMN62D0UDW: 
100k / 10p / 220:
< 40nA diff on 100uA range, >130kHz, < 30us stabilized
..
10k / 100p / 220:
< 30nA diff on 100uA range, >130kHz, < 30us stabilized
.include DMN62D0UDW.lib
.include OPAx388.LIB
.include TLV9062.lib
mosfet choice is critical: low gate charge, low Ron, low Vgsth
TODO: search edge behaviour when adding sampler circuits
0.9V max
Opamp RRio, low noise
