hb020/batterymeter/ltspice/clipsearch.asc

C1: cap; 10p
M1: nmos; PMV60ENEA
M2: nmos; PMV60ENEA
M3: nmos; PMV60ENEA
R1: res; 220
R2: res; 0.2
R3: res; 9
R4: res; 90
R5: res; 1
R6: res; 100k
U1: opamp2; OPAx388
V1: voltage; 3; Rser=2
V2: voltage; PULSE(0 0.5 1n 1f 1f 1m 2m)
V3: voltage; 0
V4: voltage; PULSE(0 3 0.5m 1f 1f 0.5m 2m)
V5: voltage; 3.3
V6: voltage; 0
V7: voltage; ""; AC 1
Named nets: 0, BN, BP, A, B
.tran 4ms
.ac dec 100 1 1MEG
AC test: 
V7 = AC 1
V(A)/V(B)
Distortion: 
(I(R2) + I(R5))/I(R2)
or
I(R2)+I(R5)-I(R1)
R6/C1/R1/PMV60ENEA: 
100k / 10p / 220:
5mA:   1.4uA diff,  180kHz
50mA:  1.4uA diff, 180kHz 
500mA: 1.6uA diff, 160kHz
.include us6k1.lib
.include OPAx388.LIB
.include PMV60ENEA.lib
TODO: search edge behaviour on amp changes
