hb020/batterymeter/ltspice/input.asc

C1: cap; 100µF
D1: schottky
D2: schottky
I1: current; 50p
R1: res; 10Meg
R2: res; 680
R3: res; 47
S1: sw; MYSW
V1: voltage; PULSE(0 25 1m 1p 1p 0.5)
V2: voltage; 3.3
V3: voltage; PULSE(0 1 0.1 1f 1f 0.2 0.5)
V4: voltage; 1.25
Named nets: 0
.tran 1s
.model MYSW SW(Ron=4 Roff=100Meg Vt=.5 Vh=-.4)
