hb020/batterymeter/ltspice/powercontrol.asc

A3: or; Vhigh=1.5
A4: schmitt; Vhigh=1.5 Vt=0.75 Vh=0.225
A5: schmitt; Vhigh=1.5 Vt=0.75 Vh=0.225
B1: bv; V=delay(V(NOT_EN),100us)
C23: Cap; 100n
C32: Cap; 10µ
M1: nmos; 2N7002
R2: Res; 1k
R36: Res; 47k
R40: Res; 1k
R66: Res; 330k
R67: Res; 470k
R69: Res; 10Meg
S1: sw; MYSW
V2: voltage; 1.5
V3: voltage; PULSE(0 1 1m 1u 1u 5s)
Named nets: 0, NOT_EN, VBAT, PWR_ON, PWR_OFF, EN
.tran 20s
.model MYSW SW(Ron=1 Vt=.5)
