hb020/batterymeter/ltspice/sinewave.asc

C6: cap; 100µ
C7: cap; 100µ
C8: cap; 1f
C9: cap; 1f
R4: res; 1k
R5: res; 100k
R6: res; 100k
R12: res; 10Meg
R13: res; 10Meg
U1: AD8691
U2: AD8691
U3: opamp2; OPAx388
U4: opamp2; OPAx388
V2: voltage; 3.3
V3: voltage; 0
V4: voltage; 0
V5: voltage; 1.65
V6: voltage; ""; AC 1
Named nets: 0, LPF0, PSU, INP, INN, MIDP, MIDN, INP_O, INN_O
.tran .1s
.noise V(MIDP) V2 DEC 1000 0.01 2k
outside of AC analysis: 
V3: SINE(0 5m 1k)
V4: PULSE(0 0.5 1u 1u 1u 12.5m 20m) / SINE(0 1 50)
.ac dec 1000 0.001 1MEG
1k + 100k on only 1 stage = about 200x amplification, noise numbers to be investigated, but look acceptable
differential amp: 1k + 100k = about 200x
OPAx388
input V range: -0.1 .. VCC + 0.1V
output V range: 20mV (10k Ohm load)
AD8691
input V range: -0.3 .. VCC - 1V
output V range: 0.4V .. VCC - 0.4V
AD8647/AD8646
input V range: 0 .. VCC
output V range: 10mV (1mA)
OPAx388: 
1kHz noise: 1.075uV/trHz
-3dB: 51kHz
AD8691: 
1kHz noise: 1.4uV/rtHz
-3dB: 54kHz
AD8646: 
1kHz noise: 1.2uV/trHz
-3dB: 150kHz
.include OPAx388.LIB
.include AD8646.lib
10mV pk-pk in, 2V pk-pk out
