hb020/batterymeter/ltspice/voltagesense.asc

D1: schottky; BAT54
D2: schottky; BAT54
J1: njf; 2N5484
R1: res; 470k
R2: res; 1Meg
V1: voltage; PULSE(0 5 0 0.5 1f 1)
V2: voltage; 1.2
Named nets: 0
.include DMN62D0UDW.lib
.tran .5s
